kevincw01/smart-water-pressure-sensor/nano_33_mqtt_water_pressure/credentials.h

char networkSSID[] = "YOUR_SSID";
char networkPASSWORD[] = "YOUR_WIFI_PASSWORD";
char mqttSERVER[] = "YOUR_MQTT_SERVER_IP";
char mqttUSERNAME[] = "YOUR_MQTT_SERVER_USERNAME";
char mqttPASSWORD[] = "YOUR_MQTT_SERVER_PASSWORD";

char pubTopicPOST[] = "/sensor/water-pressure"; 
